afoxinsocks/foxie-clock/images/case_render1.png

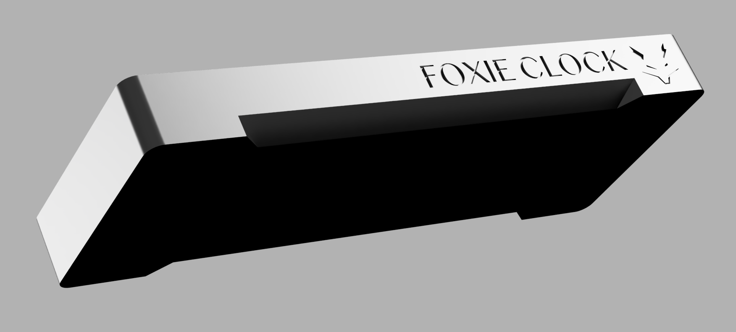
images/case_render1.png
