afoxinsocks/foxie-clock/images/case_render3.png

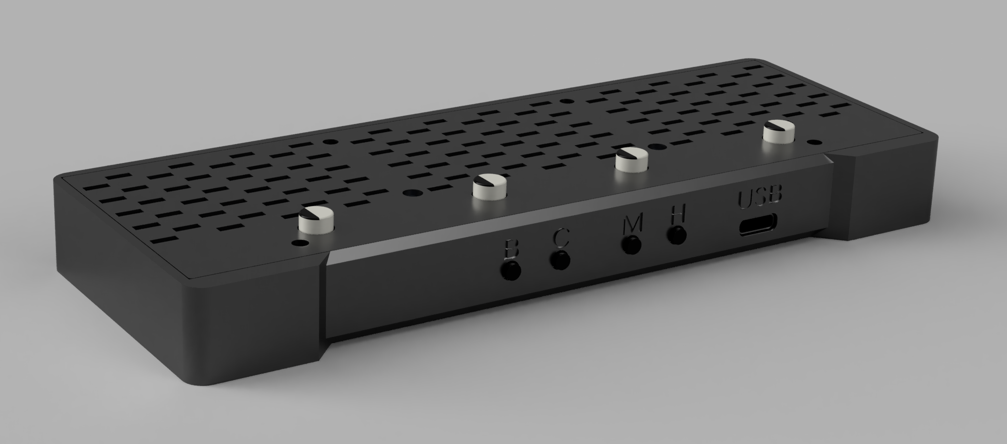
images/case_render3.png
