afoxinsocks/foxie-clock/images/pcb_render.png

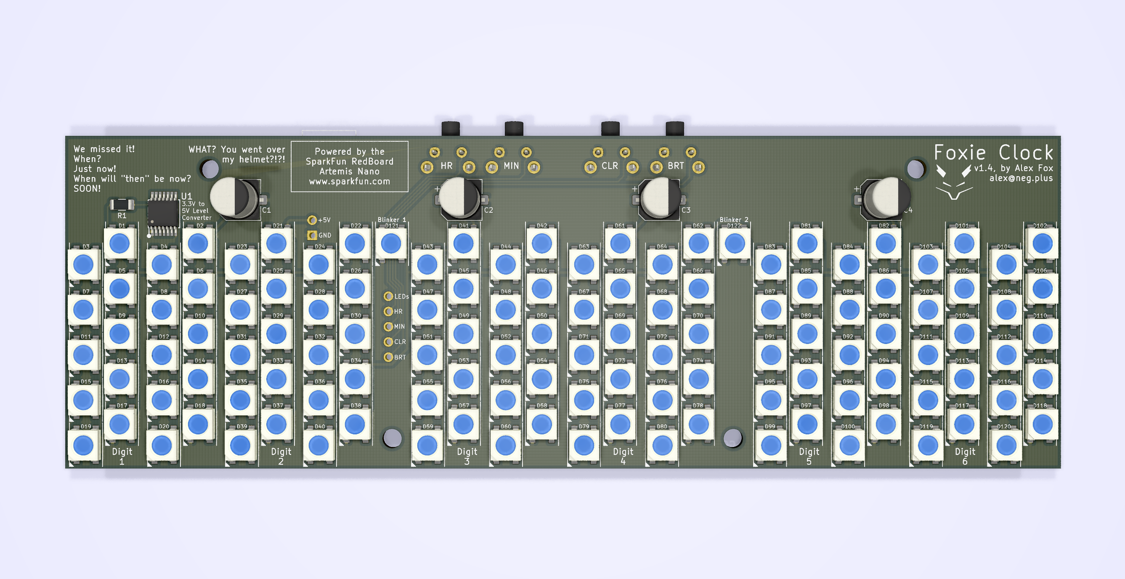
images/pcb_render.png
