afoxinsocks/foxie-clock/images/assembly_step8d.jpg

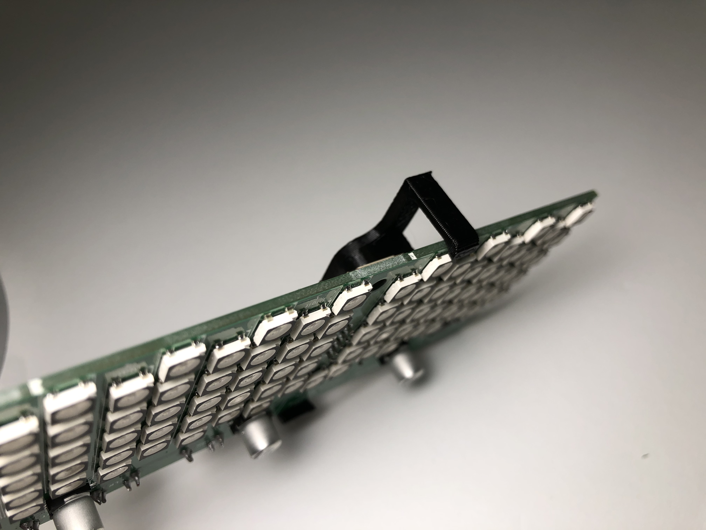
images/assembly_step8d.jpg
