afoxinsocks/foxie-clock/images/assembly_step12c.jpg

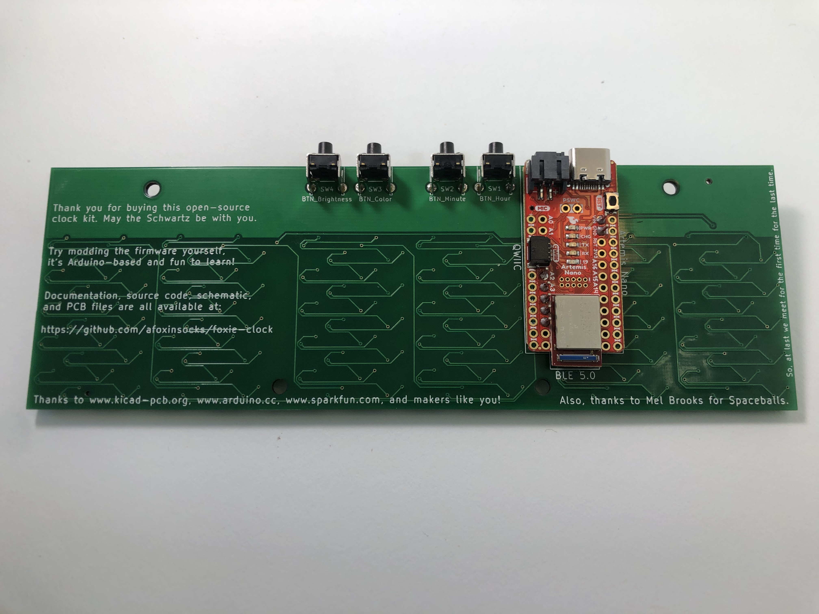
images/assembly_step12c.jpg
