afoxinsocks/foxie-clock/firmware/settings.hpp

#pragma once
#include <EEPROM.h>

// Note: If adding new settings, ALWAYS ADD AT THE END OF THE LIST.
// Otherwise, settings will be loaded from the wrong location and have
// the wrong value
enum SettingNames_e
{
    SETTING_DIGIT_TYPE = 0,
    SETTING_CUR_BRIGHTNESS,
    SETTING_MIN_BRIGHTNESS,
    SETTING_MAX_BRIGHTNESS,
    SETTING_BLINKING_SEPARATORS,
    SETTING_COLOR,
    SETTING_ANIMATION_TYPE,
    SETTING_24_HOUR_MODE,
    SETTING_FLIP_DISPLAY,
    SETTING_TRANSITION_TYPE,

    // Add new settings here

    // Do not add settings after this line
    TOTAL_SETTINGS,
};

// The purpose of this class is to store user configurable settings
// into EEPROM (including emulated EEPROM stored in flash), only storing
// when all values have been updated to save write cycles when possible.
//
// For simplicity, every value stored will be a uint32_t, restricting us
// to 256 total settings.
class Settings
{
  private:
    enum
    {
        SETTINGS_SIZE = 256, // 256 4-byte values, 1024 bytes total on Artemis
    };

    uint32_t m_storage[SETTINGS_SIZE] = {0};

  public:
    Settings()
    {
        Load();

        // This happens on a new board since the EEPROM has never been written.
        if (Get(SETTING_DIGIT_TYPE) > DT_PIXELS)
        {
            Reset();
        }
    }

    void Reset()
    {
        Set(SETTING_DIGIT_TYPE, 1); // 1 is edge lit (acrylics), 2 is pixel display
        Set(SETTING_CUR_BRIGHTNESS, 64);
        Set(SETTING_MIN_BRIGHTNESS, 4);
        Set(SETTING_MAX_BRIGHTNESS, 192);
        Set(SETTING_BLINKING_SEPARATORS, 1);
        Set(SETTING_COLOR, 192);
        Set(SETTING_ANIMATION_TYPE, 1);
        Set(SETTING_24_HOUR_MODE, 0);
        Set(SETTING_FLIP_DISPLAY, 0);
        Set(SETTING_TRANSITION_TYPE, 1);

        Save();
    }

    // only call after all settings have been updated
    void Save()
    {
#ifdef FOXIE_ARTEMIS
        // for Artemis, we're going to write the entire block at once
        // to save write cycles
        const size_t blockSize = SETTINGS_SIZE * sizeof(uint32_t);
        const size_t maxAllowedSize = blockSize;
        writeBlockToEEPROM(0, (const uint8_t *)m_storage, blockSize, maxAllowedSize);
#endif
    }

    uint32_t Get(const SettingNames_e name) const
    {
        return m_storage[(const uint32_t)name];
    }

    void Set(const SettingNames_e name, const uint32_t value)
    {
        m_storage[(const uint32_t)name] = value;
    }

  private:
    void Load()
    {
        for (size_t i = 0; i < TOTAL_SETTINGS; ++i)
        {
            EEPROM.get(i * sizeof(uint32_t), m_storage[i]);
        }
    }
};
