afoxinsocks/foxie-clock/firmware/elapsed_time.hpp

#pragma once

class ElapsedTime
{
  private:
    int m_millis{0};

  public:
    ElapsedTime()
    {
        Reset();
    }

    void Set(const int millis)
    {
        m_millis = millis;
    }

    void Reset()
    {
        m_millis = millis();
    }

    int Ms()
    {
        return ((int)millis()) - m_millis;
    }
};
